revaldinho/cpc_ram_expansion/cpc_ram_expansion/src/old_source/README

This directory contains archived old source code for the original v1.00 board and a modified (cut and rewired) version of that board used to trial the overdrive code.

** NOT TO BE USED WITH THE V1.10 CPLD BOARD **
