revaldinho/cpc_ram_expansion/cpc_eightrom/releases/v1.01/cpc_eightrom_placement.png

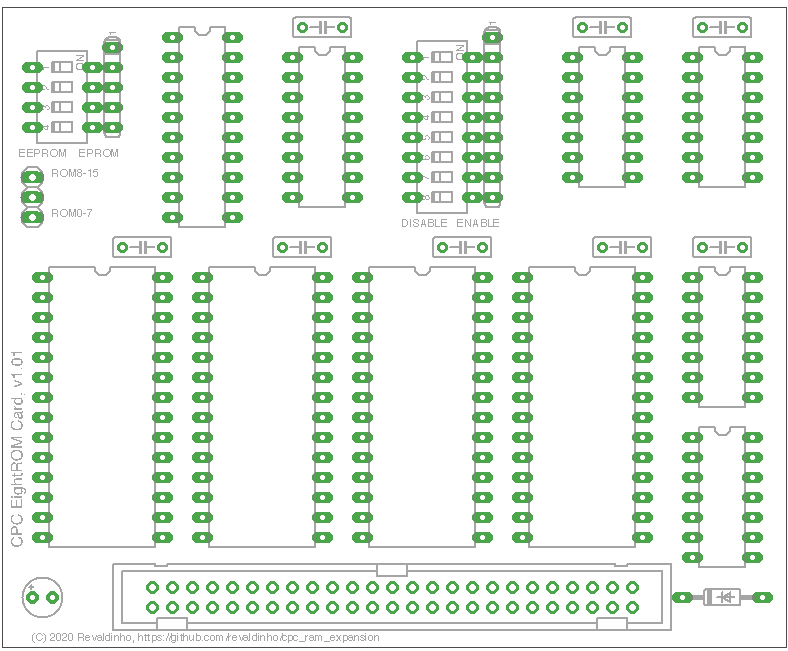
cpc_eightrom/releases/v1.01/cpc_eightrom_placement.png
