revaldinho/cpc_ram_expansion/cpc_eightrom/releases/v1.01/cpc_eightrom_placement_annotated.jpg

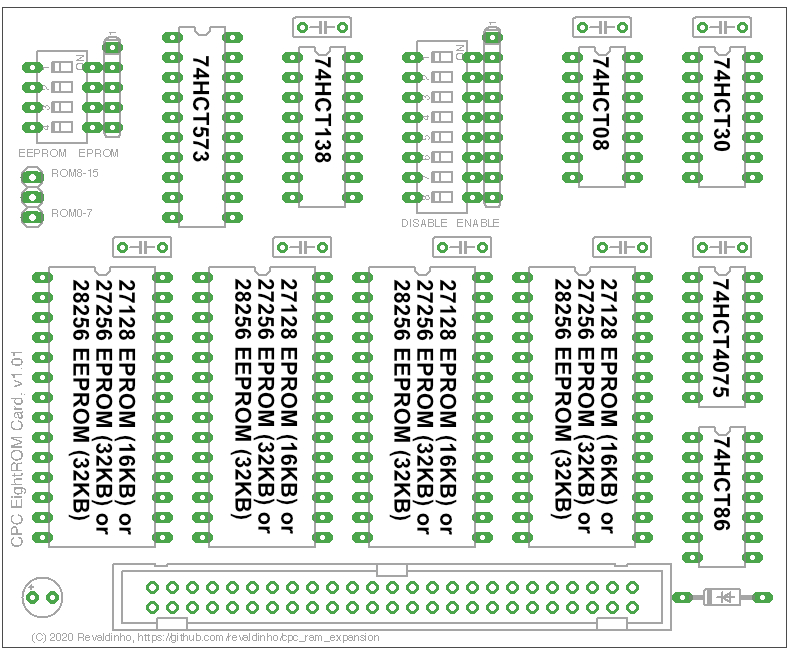
cpc_eightrom/releases/v1.01/cpc_eightrom_placement_annotated.jpg
