revaldinho/cpc_ram_expansion/cpc_ram_expansion1mb/releases/rc-3-canberra/cpc_ram1m_74series/cpc_ram1m_74_v1.00_bot.png

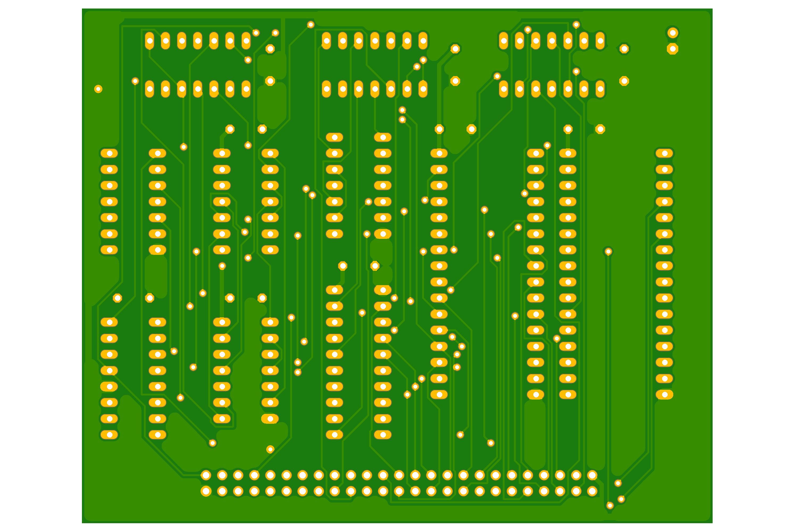
cpc_ram_expansion1mb/releases/rc-3-canberra/cpc_ram1m_74series/cpc_ram1m_74_v1.00_bot.png
