revaldinho/cpc_ram_expansion/cpc_ram_expansion1mb/releases/rc-3-canberra/cpc_ram1m_plcc84/cpc_ram1mb_plcc84_top.png

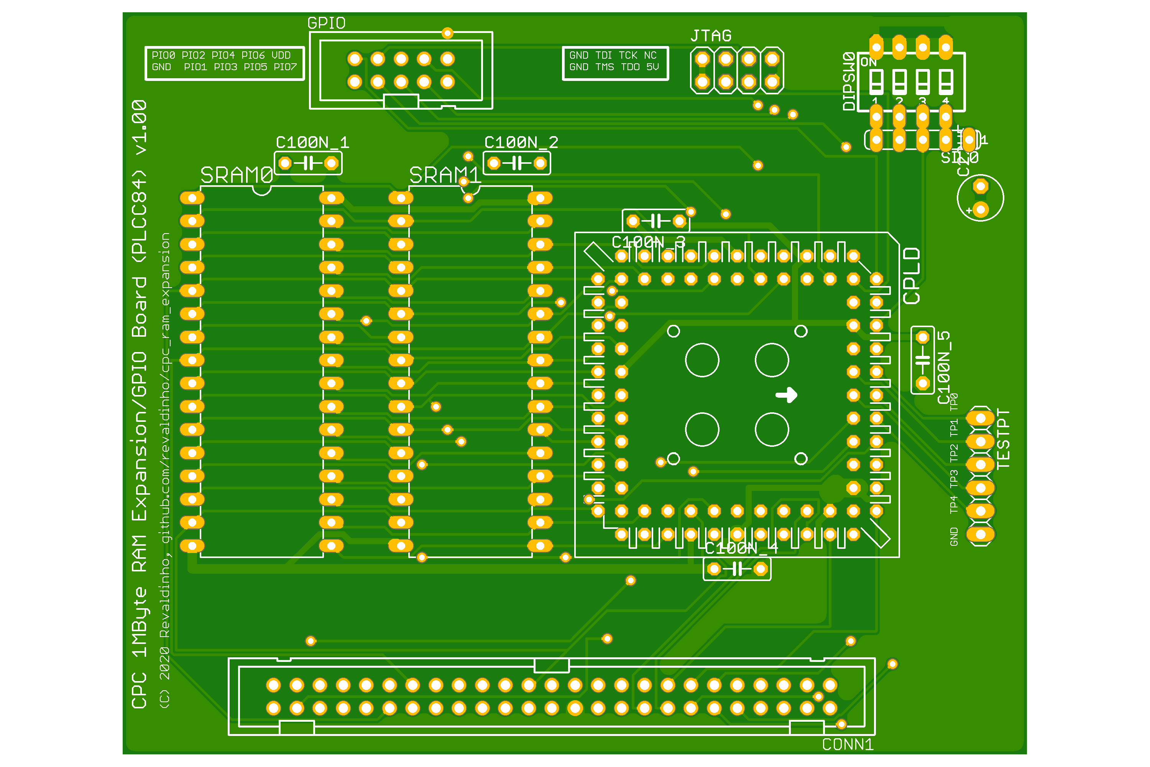
cpc_ram_expansion1mb/releases/rc-3-canberra/cpc_ram1m_plcc84/cpc_ram1mb_plcc84_top.png
