revaldinho/cpc_ram_expansion/img/CPC_1MB_RAM_SN74_photo.jpg

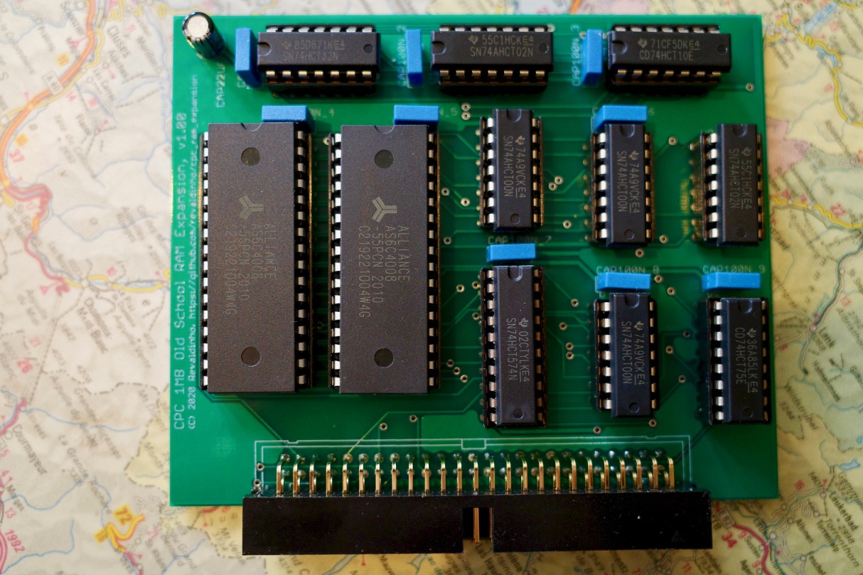
img/CPC_1MB_RAM_SN74_photo.jpg
