revaldinho/cpc_ram_expansion/img/CPC_1MB_RAM_top_v1.00.png

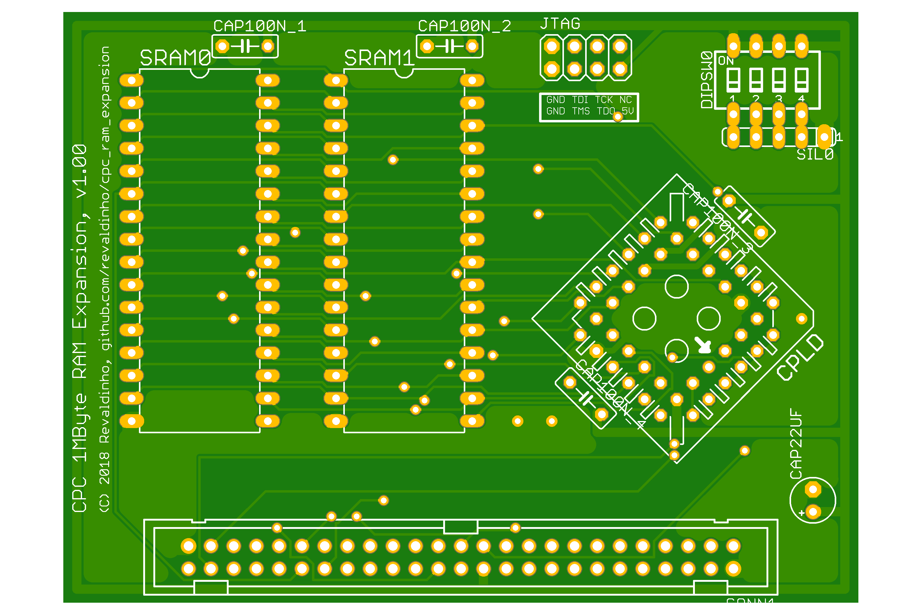
img/CPC_1MB_RAM_top_v1.00.png
