revaldinho/cpc_ram_expansion/img/CPC_512K_RAM_bot_v1.00.png

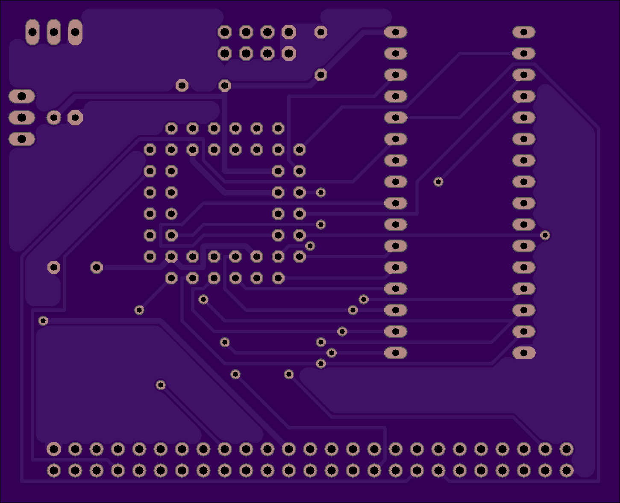
img/CPC_512K_RAM_bot_v1.00.png
