revaldinho/cpc_ram_expansion/img/CPC_512K_RAM_Eagle_top_v1.00.png

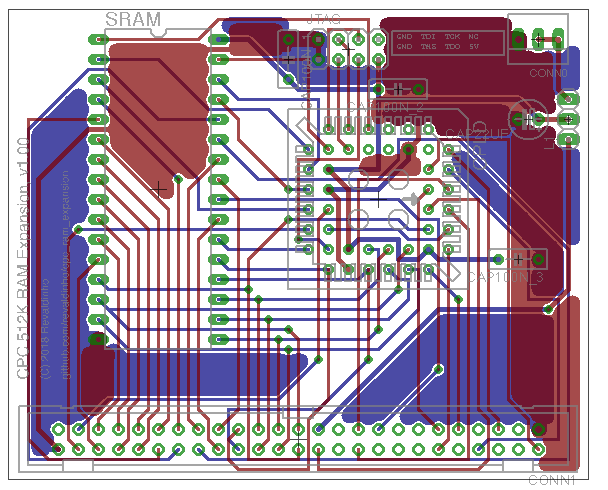
img/CPC_512K_RAM_Eagle_top_v1.00.png
