revaldinho/cpc_ram_expansion/img/CPC_512K_RAM_SN74_bot_v2.01.png

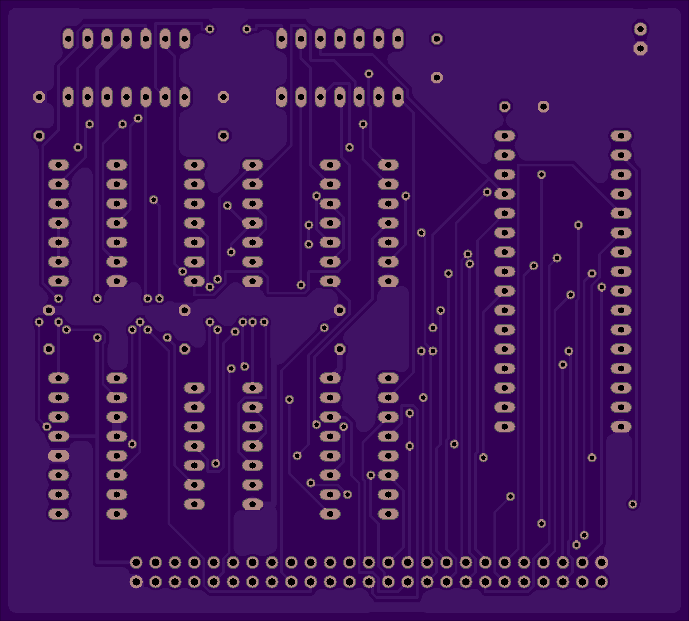
img/CPC_512K_RAM_SN74_bot_v2.01.png
