revaldinho/cpc_ram_expansion/img/CPC_512K_RAM_SN74_photo_v2.01.jpg

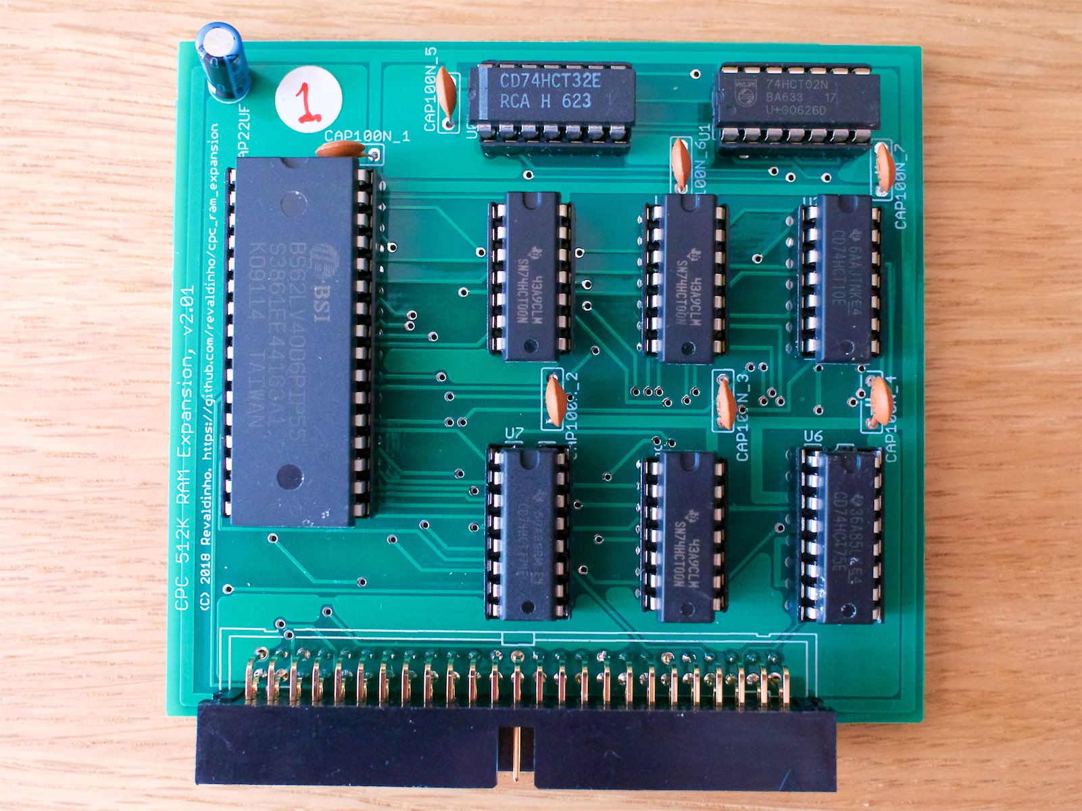
img/CPC_512K_RAM_SN74_photo_v2.01.jpg
