revaldinho/cpc_ram_expansion/img/CPC_512K_RAM_SN74_top_v2.00.png

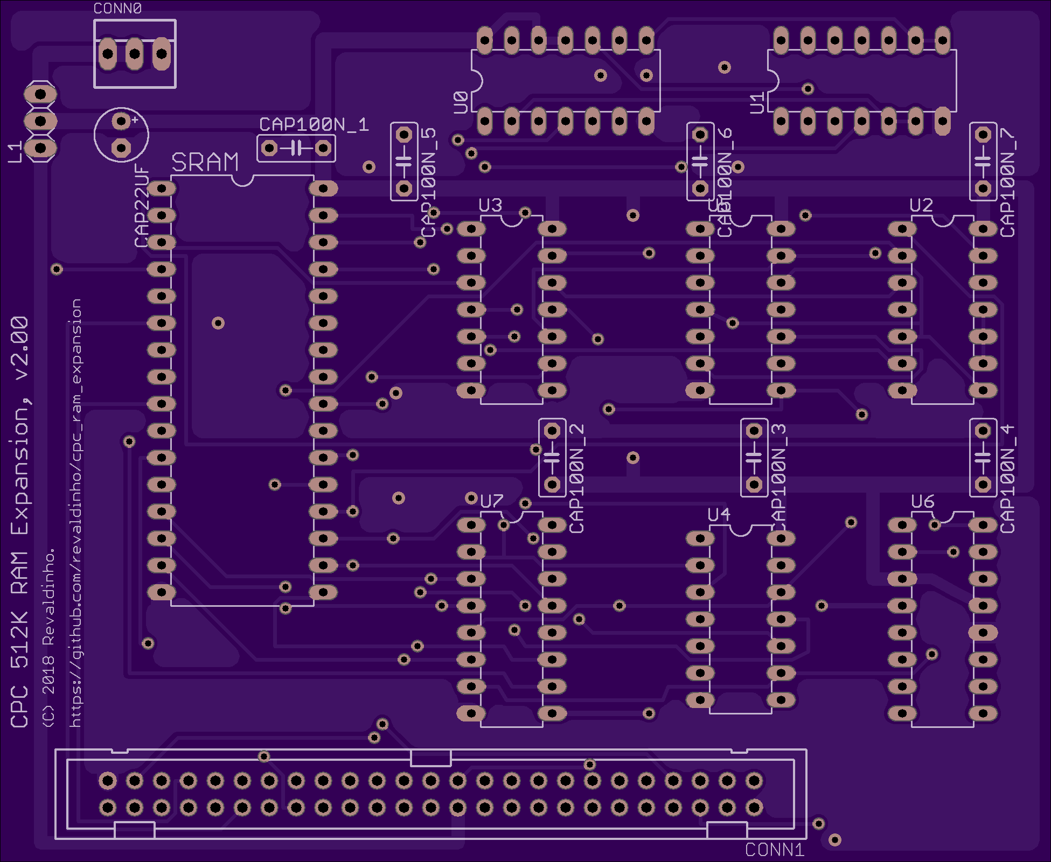
img/CPC_512K_RAM_SN74_top_v2.00.png
