revaldinho/cpc_ram_expansion/img/cpc_backplane_edge.png

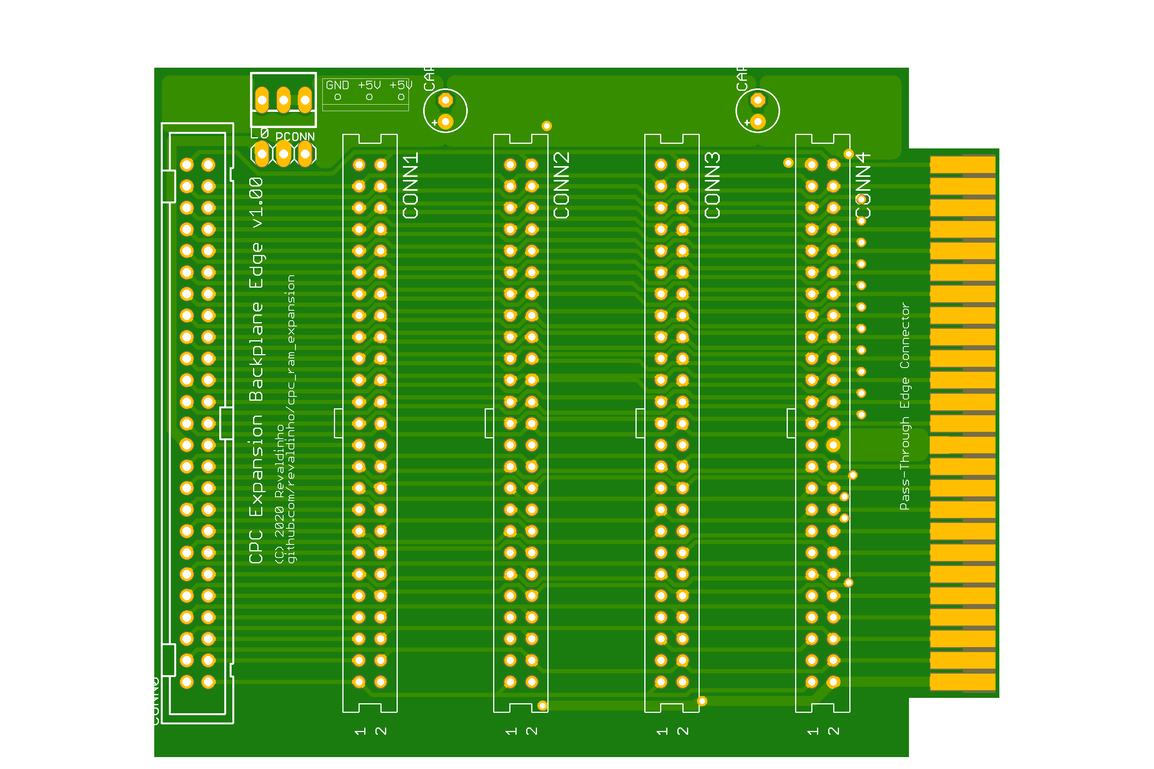
img/cpc_backplane_edge.png
