revaldinho/cpc_ram_expansion/img/cpc_backplane_edge_bot.png

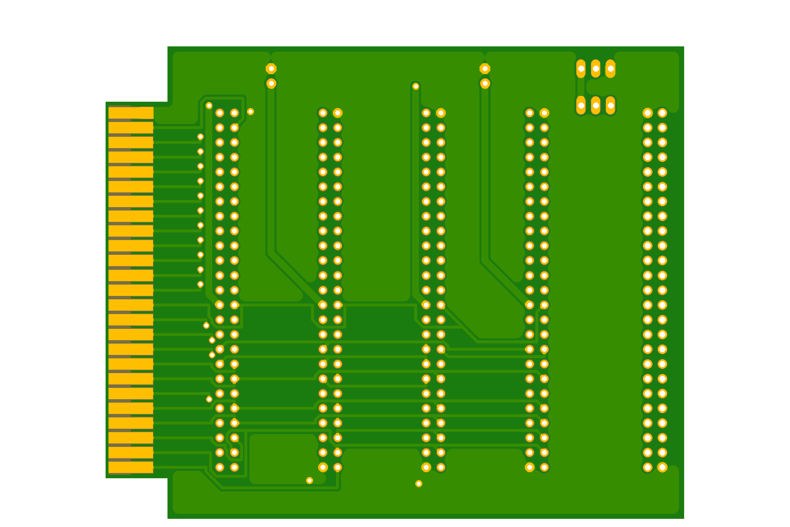
img/cpc_backplane_edge_bot.png
