revaldinho/cpc_ram_expansion/img/CPC_BACKPLANE_placement.png

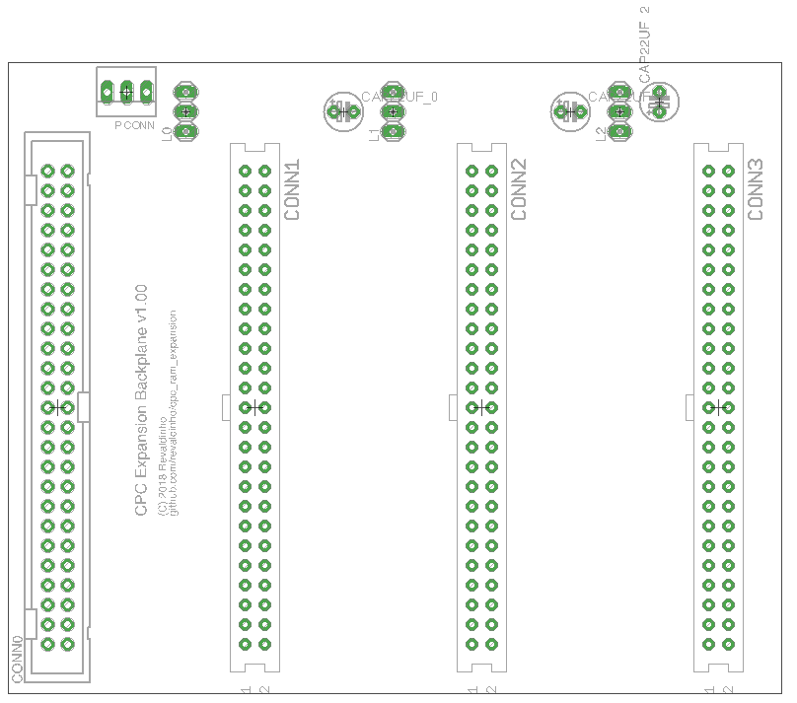
img/CPC_BACKPLANE_placement.png
