revaldinho/cpc_ram_expansion/img/CPC_BACKPLANE_top_v1.00.png

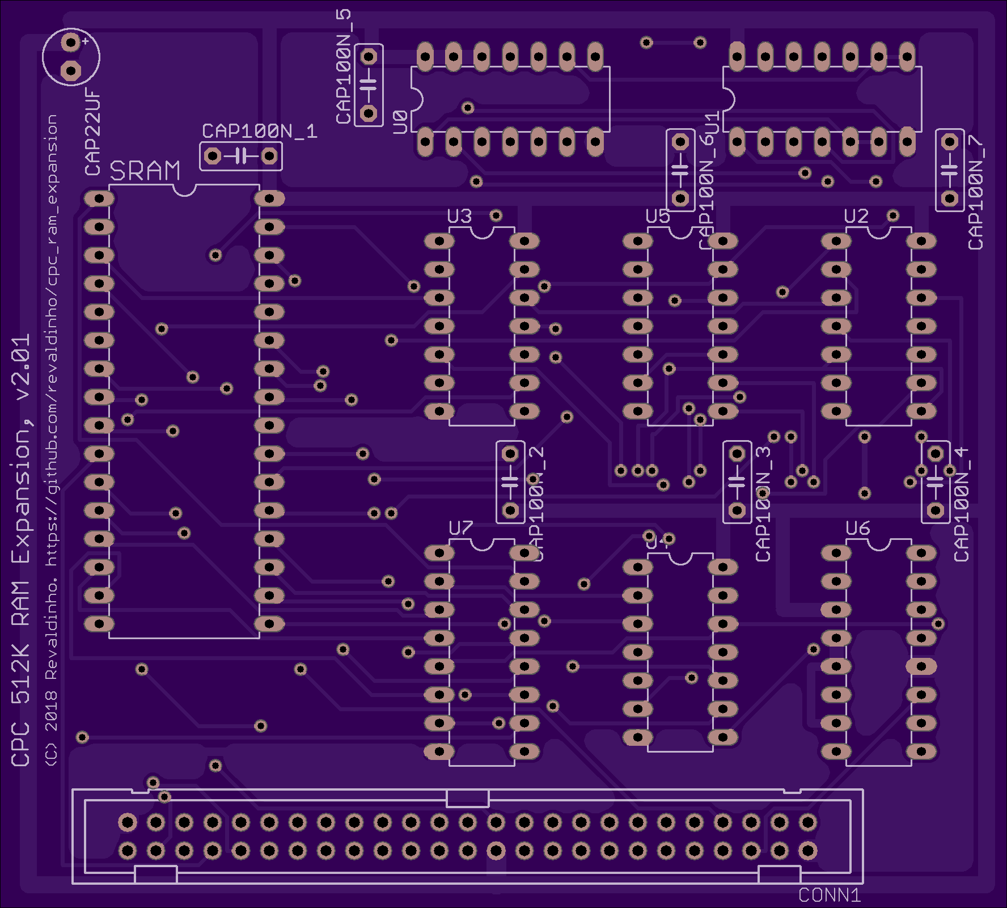
img/CPC_BACKPLANE_top_v1.00.png
