revaldinho/cpc_ram_expansion/img/CPC_BACKPLANE_v1.10_placement.png

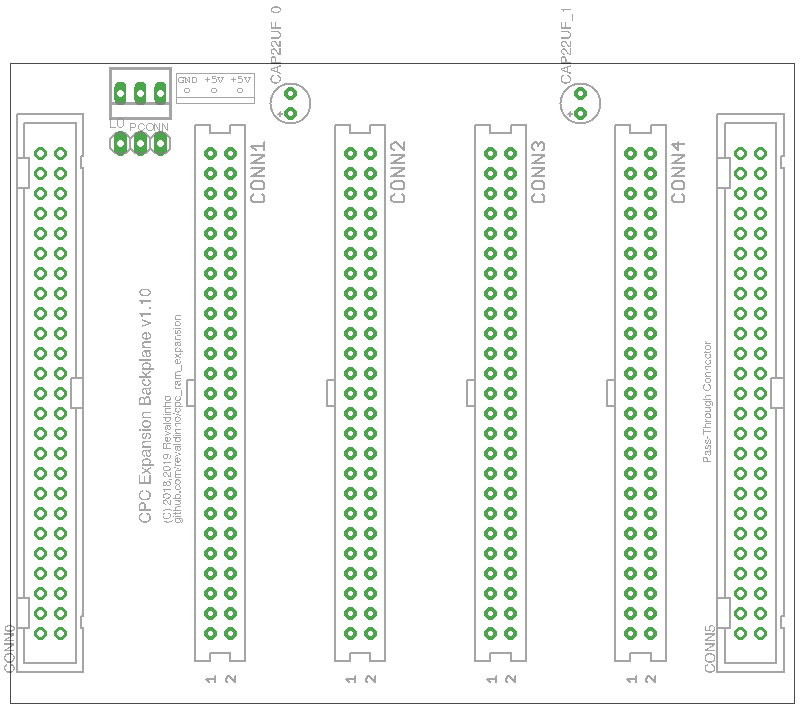
img/CPC_BACKPLANE_v1.10_placement.png
