revaldinho/cpc_ram_expansion/img/CPC_Exp_card_family_photo 1.jpg

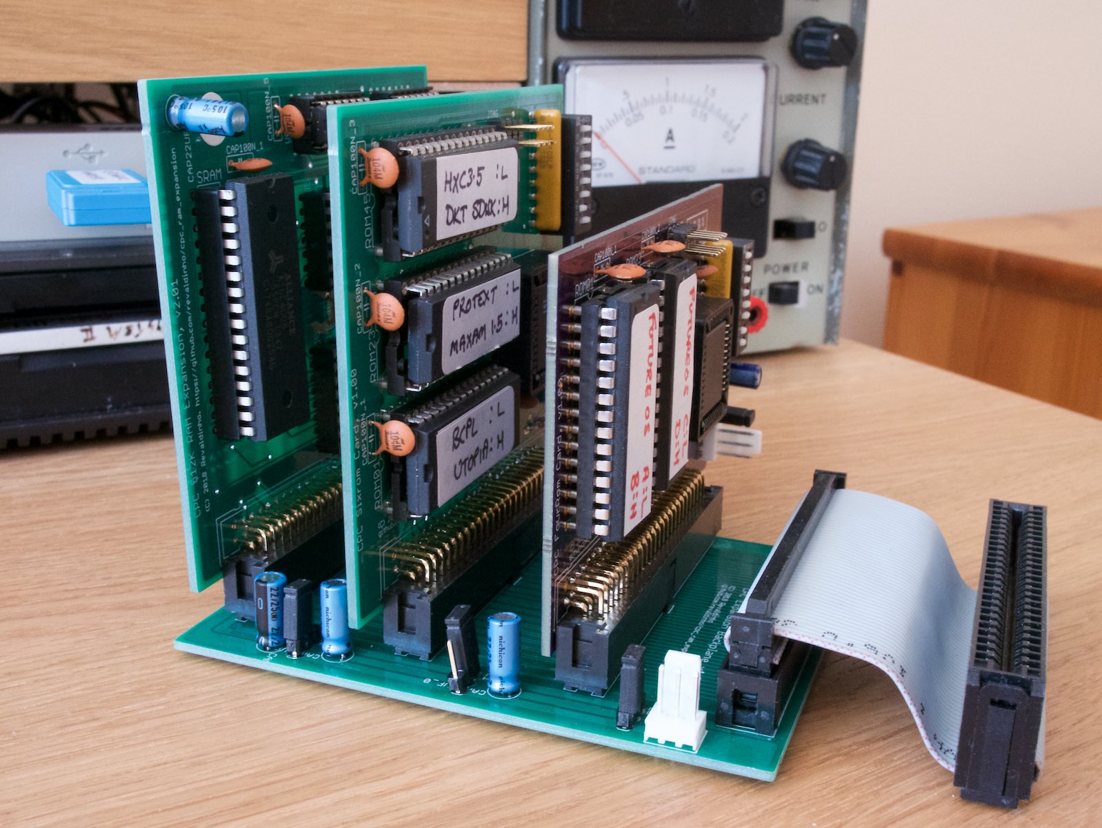
img/CPC_Exp_card_family_photo 1.jpg
