revaldinho/cpc_ram_expansion/img/CPC_Exp_card_family_photo 2.jpg

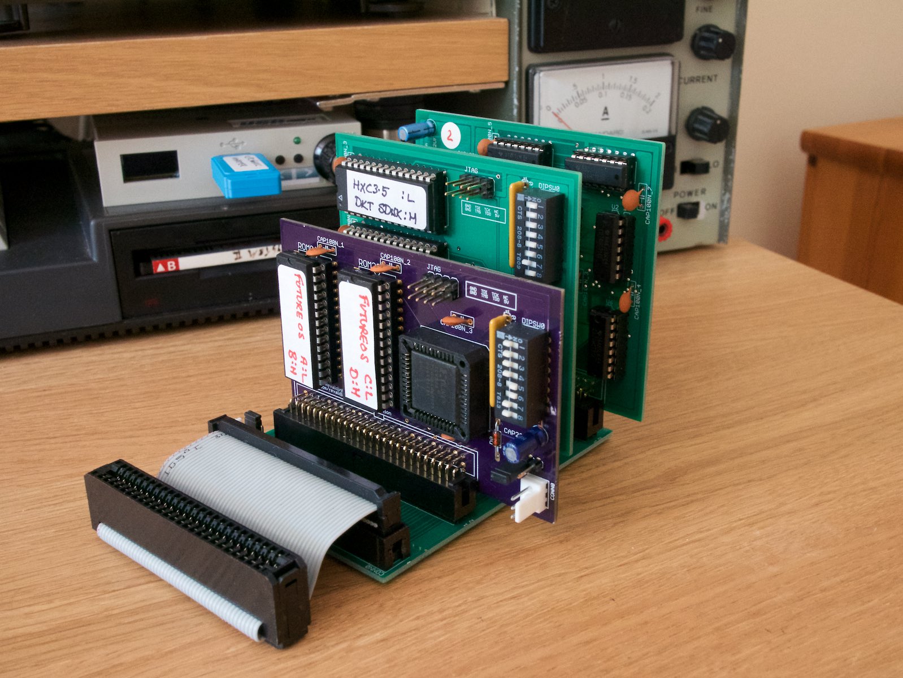
img/CPC_Exp_card_family_photo 2.jpg
