revaldinho/cpc_ram_expansion/img/CPC_FOURROM_bot_V1.00.png

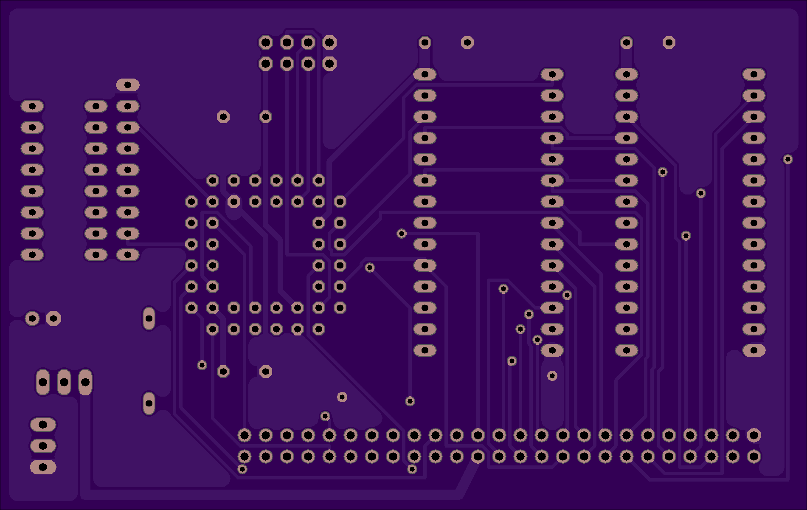
img/CPC_FOURROM_bot_V1.00.png
