revaldinho/cpc_ram_expansion/img/CPC_FOURROM_photo.jpg

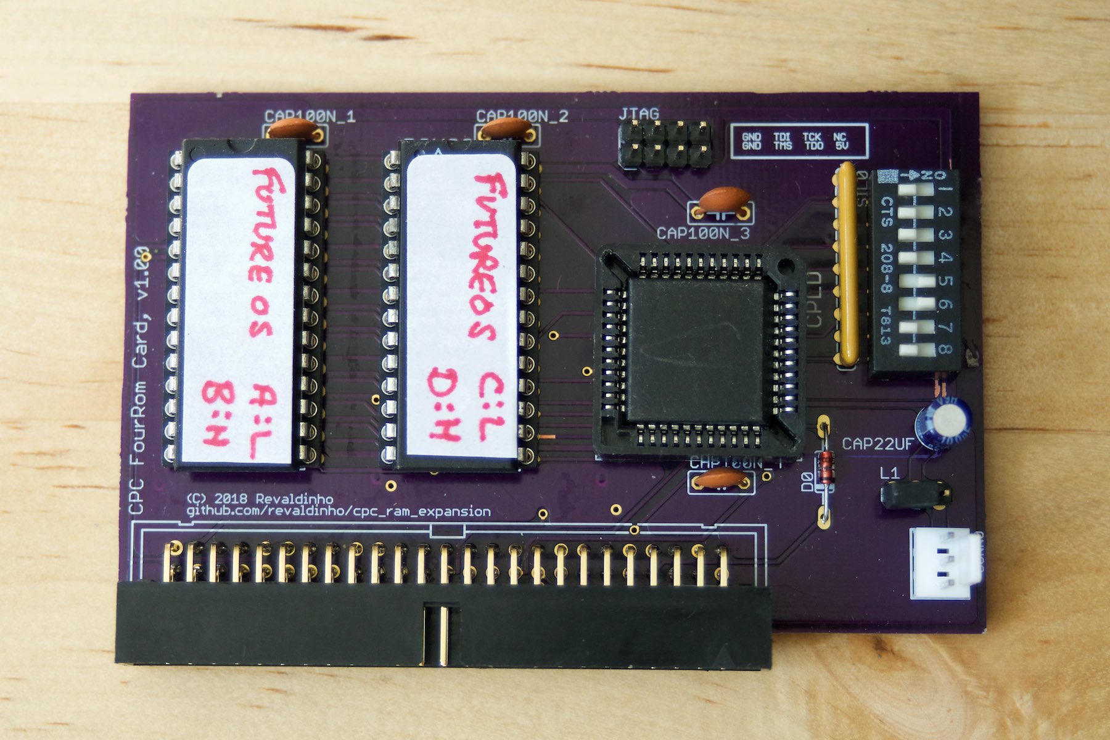
img/CPC_FOURROM_photo.jpg
