revaldinho/cpc_ram_expansion/img/CPC_FOURROM_place.png

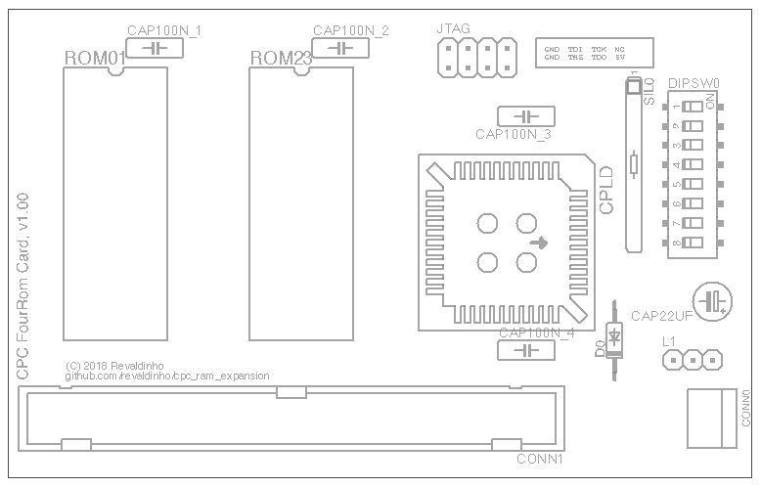
img/CPC_FOURROM_place.png
