revaldinho/cpc_ram_expansion/img/CPC_SIXROM_Eagle_V1.00.png

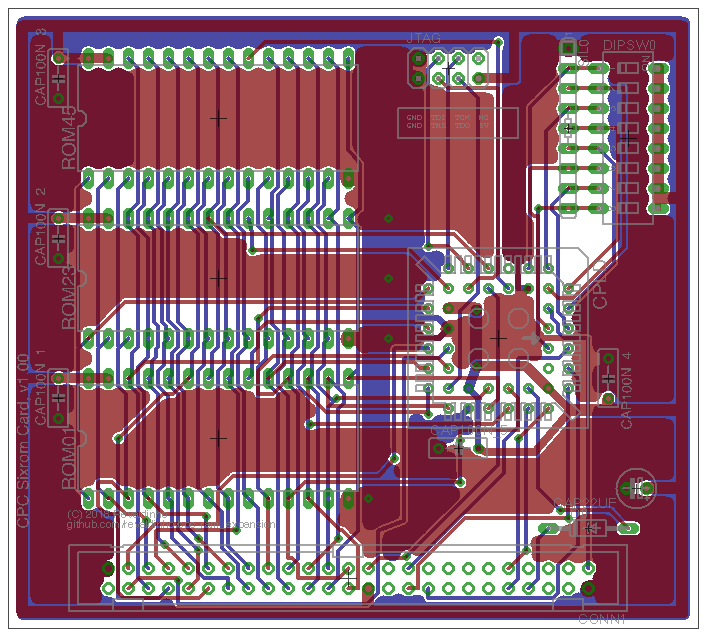
img/CPC_SIXROM_Eagle_V1.00.png
