revaldinho/cpc_ram_expansion/img/CPC_SIXROM_photo1.jpg

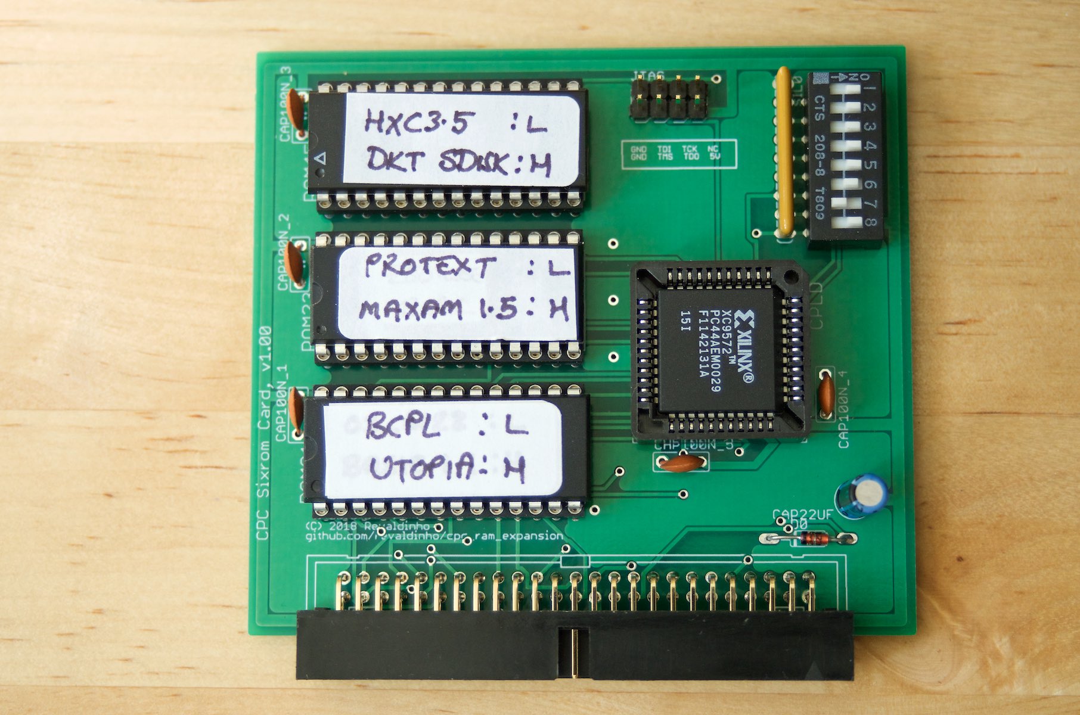
img/CPC_SIXROM_photo1.jpg
