revaldinho/cpc_ram_expansion/img/CPC_SIXROM_V1.00_bot.png

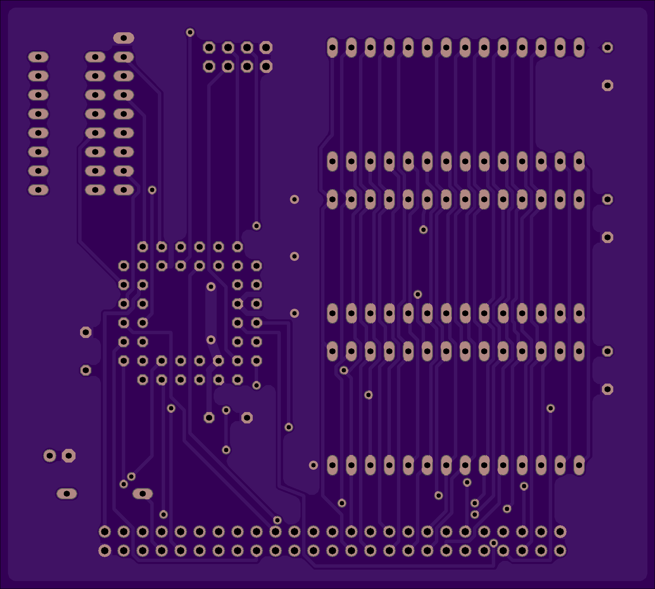
img/CPC_SIXROM_V1.00_bot.png
