revaldinho/cpc_ram_expansion/img/CPC_SIXROM_V1.10_photo.jpg

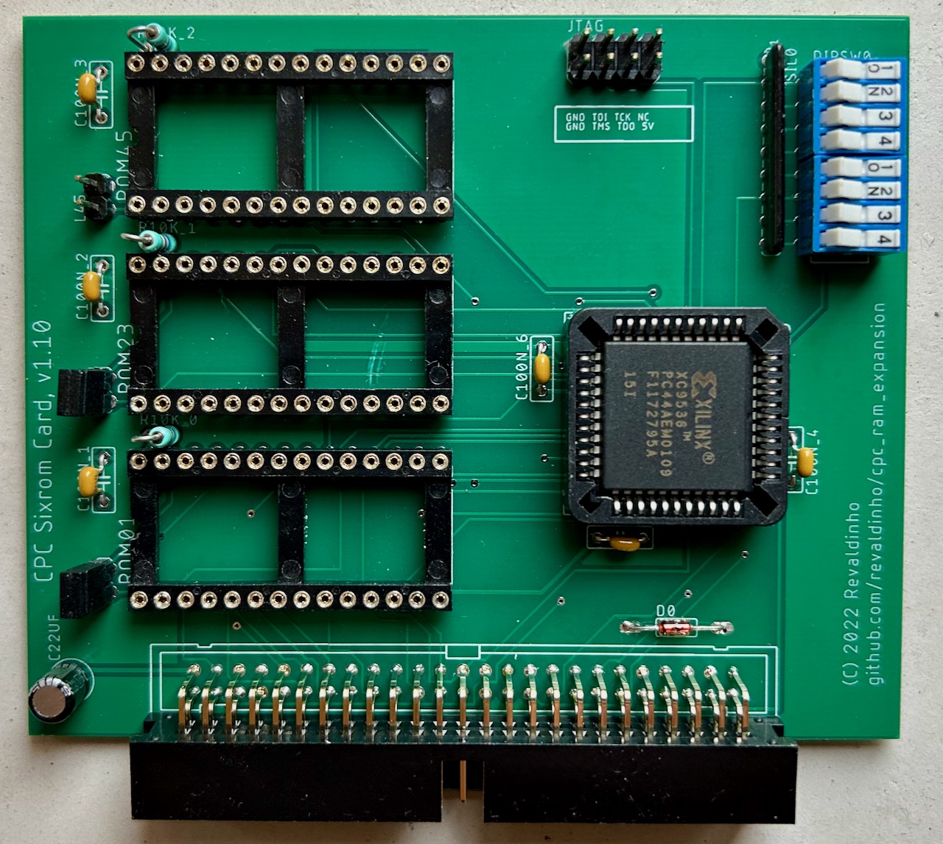
img/CPC_SIXROM_V1.10_photo.jpg
