revaldinho/cpc_ram_expansion/img/CPC_SIXROM_V1.10_place.png

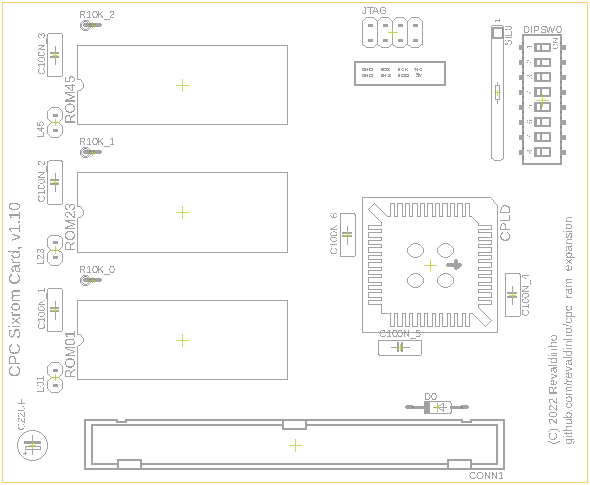
img/CPC_SIXROM_V1.10_place.png
