revaldinho/cpc_ram_expansion/img/CPC_UNIVERSAL_RAM512K.jpg

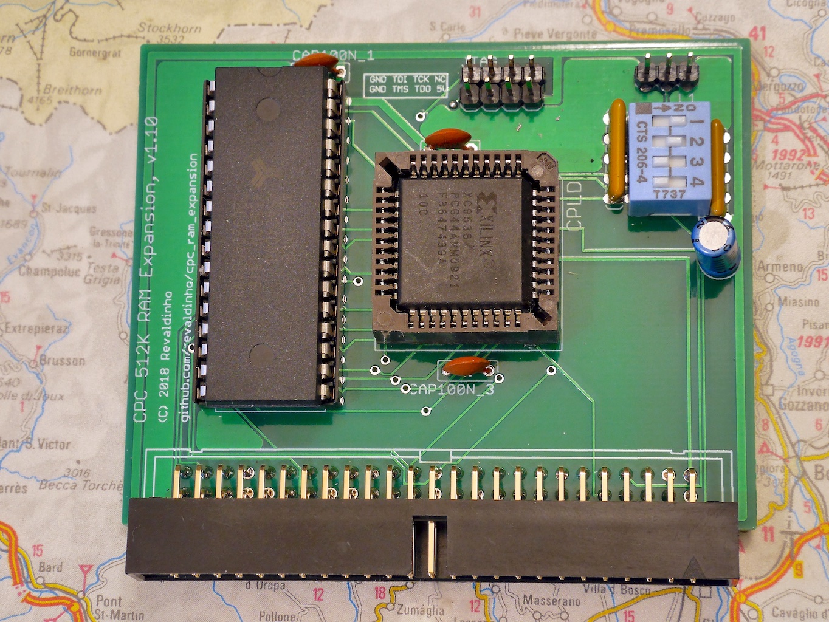
img/CPC_UNIVERSAL_RAM512K.jpg
