revaldinho/cpc_ram_expansion/img/EightROM_board.jpeg

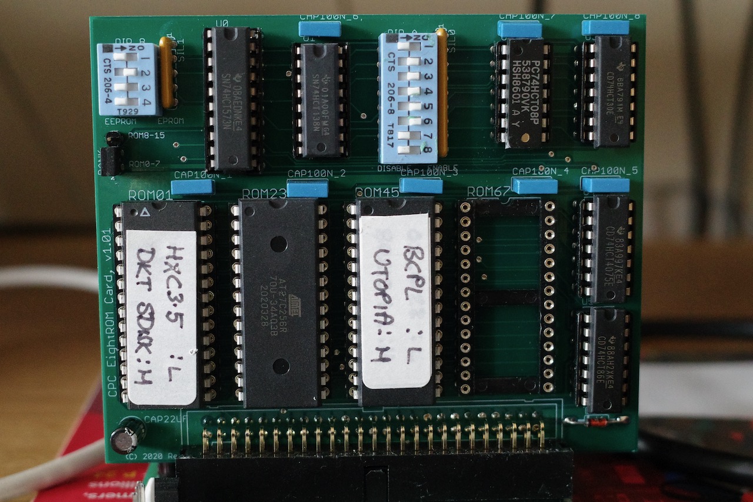
img/EightROM_board.jpeg
