revaldinho/cpc_ram_expansion/img/EightROM_with_display.jpeg

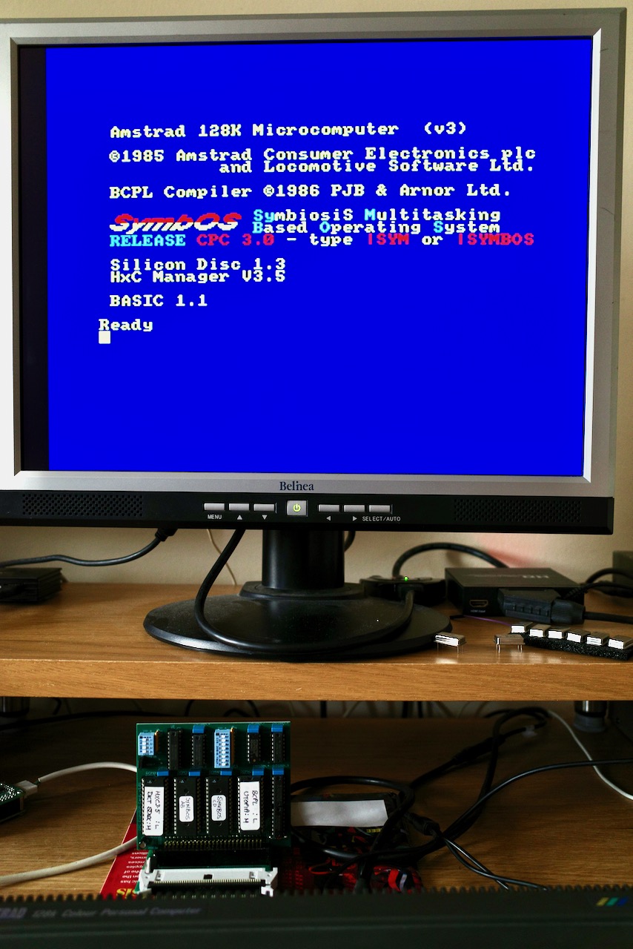
img/EightROM_with_display.jpeg
