revaldinho/cpc_ram_expansion/img/FourSlotEdgeExpansion.jpg

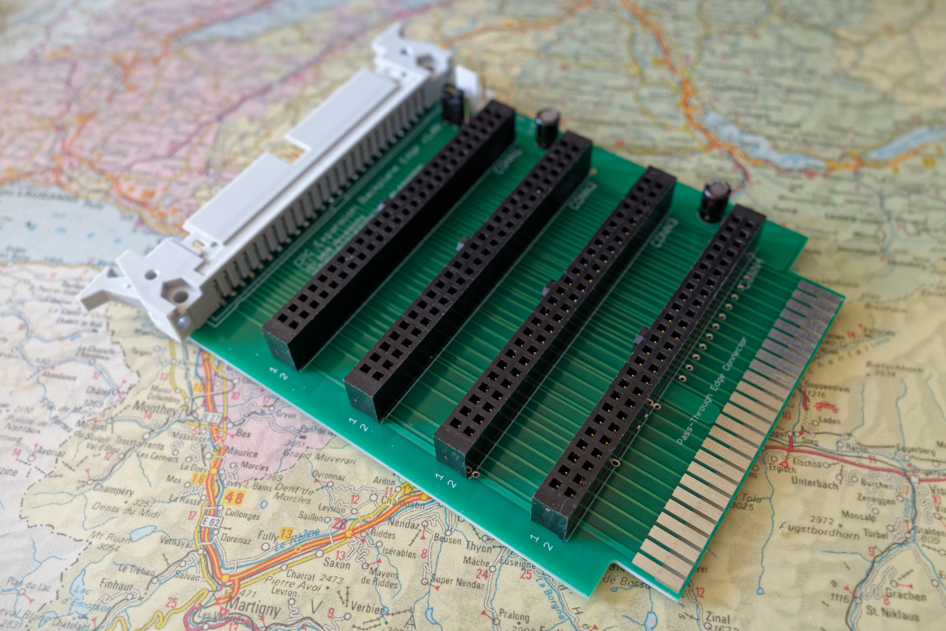
img/FourSlotEdgeExpansion.jpg
