revaldinho/cpc_ram_expansion/img/protoboard.jpg

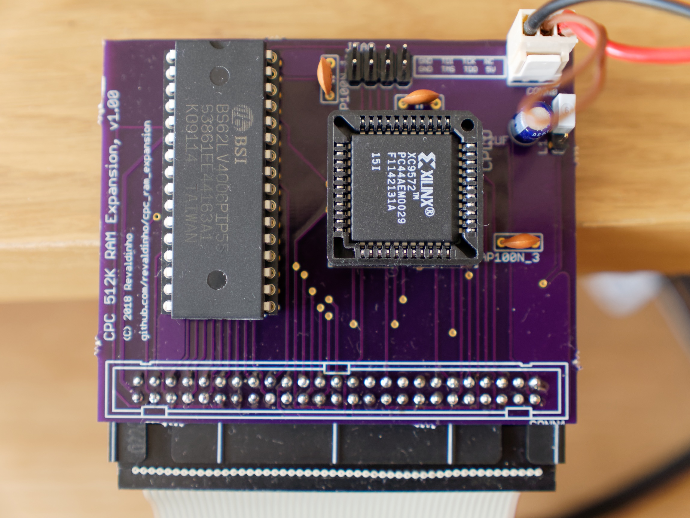
img/protoboard.jpg
