revaldinho/cpc_ram_expansion/img/T35_ROMBOARD_Eagle_V1.00_top.png

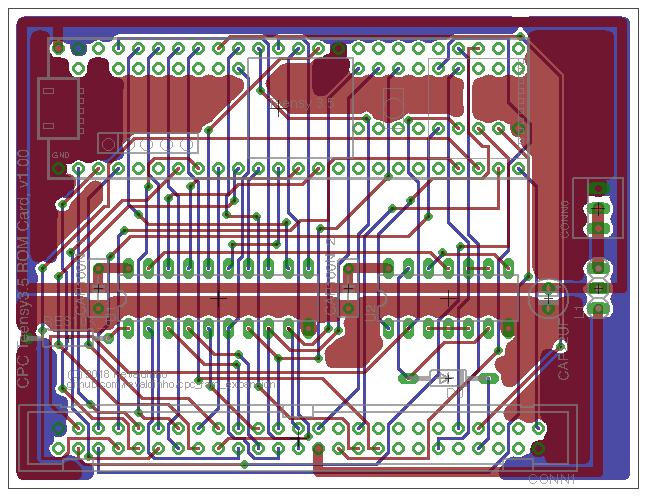
img/T35_ROMBOARD_Eagle_V1.00_top.png
