revaldinho/cpc_ram_expansion/img/T35_ROMBOARD_V1.10_bot.png

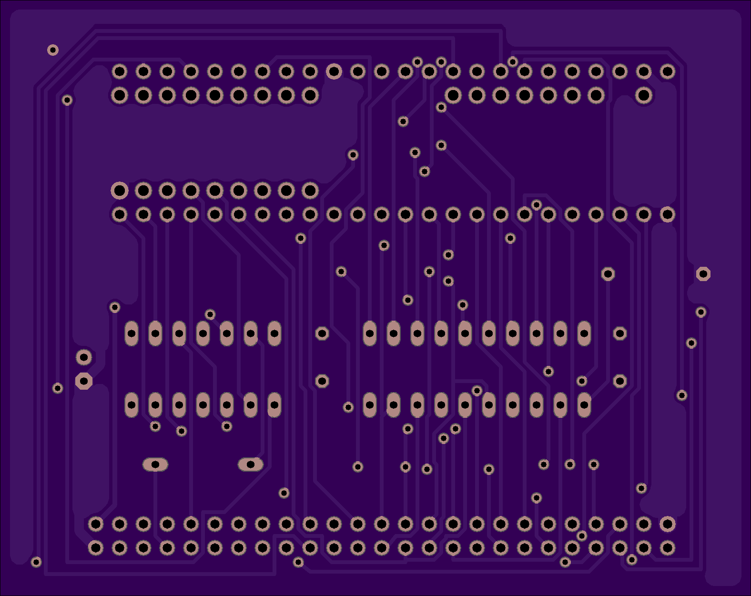
img/T35_ROMBOARD_V1.10_bot.png
