revaldinho/cpc_ram_expansion/cpc_backplane/pcb/cpc_backplane5.v

//
//
// netlister.py format
//
// (c) Revaldinho, 2018
//
//
// Unbuffered board - assume power and signal buffering is done on a dedicated board.
//
// 2018-08-12 Add 4th connector and simplify external power connections

module cpc_backplane5 ();

  // wire declarations
  supply0 VSS;
  supply1 VDD_CPC;
  supply1 VDD_EXT;
  supply1 VDD1;


  special_wire CLK, RESET_B, BUSRESET_B;

  wire Sound;
  wire A15,A14,A13,A12,A11,A10,A9,A8,A7,A6,A5,A4,A3,A2,A1,A0 ;
  wire D7,D6,D5,D4,D3,D2,D1,D0 ;
  wire MREQ_B;
  wire M1_B;
  wire RFSH_B;
  wire IOREQ_B;
  wire RD_B;
  wire WR_B;
  wire HALT_B;
  wire INT_B ;
  wire NMI_B ;
  wire BUSRQ_B;
  wire BUSACK_B;
  wire READY;
  wire ROMEN_B;
  wire ROMDIS ;
  wire RAMRD_B;
  wire RAMDIS;
  wire CURSOR;
  wire LPEN;
  wire EXP_B;





  // 3 pin header with link to use either CPC or external 5V power for the board
  hdr1x03      L0 (
                   .p1(VDD_CPC),
                   .p2(VDD1),
                   .p3(VDD_EXT)
                   );

  PJ057A  PCONN (
                 .centre(VDD_EXT),
                 .barrel1(VSS),
                 .barrel2(VSS)
                 );

//  // Radial electolytics
//  cap22uf         C0(.minus(VSS),.plus(VDD1));
//  cap22uf         C1(.minus(VSS),.plus(VDD1));

  // Amstrad CPC Edge Connector
  //
  // V1.01 Corrected upper and lower rows for male header.

  idc_hdr_50w  CONN0 (
                      .p50(Sound),   .p49(VSS),
                      .p48(A15),     .p47(A14),
                      .p46(A13),     .p45(A12),
                      .p44(A11),     .p43(A10),
                      .p42(A9),      .p41(A8)
                      .p40(A7),      .p39(A6),
                      .p38(A5),      .p37(A4),
                      .p36(A3),      .p35(A2),
                      .p34(A1),      .p33(A0),
                      .p32(D7),      .p31(D6)
                      .p30(D5),      .p29(D4),
                      .p28(D3),      .p27(D2),
                      .p26(D1),      .p25(D0),
                      .p24(VDD_CPC), .p23(MREQ_B),
                      .p22(M1_B),    .p21(RFSH_B),
                      .p20(IOREQ_B), .p19(RD_B),
                      .p18(WR_B),    .p17(HALT_B),
                      .p16(INT_B),   .p15(NMI_B),
                      .p14(BUSRQ_B), .p13(BUSACK_B),
                      .p12(READY),   .p11(BUSRESET_B),
                      .p10(RESET_B), .p9 (ROMEN_B),
                      .p8 (ROMDIS),  .p7 (RAMRD_B),
                      .p6 (RAMDIS),  .p5 (CURSOR),
                      .p4 (LPEN),    .p3 (EXP_B),
                      .p2 (VSS),     .p1 (CLK)
                      ) ;

  // Female sockets have pins reversed by orientation on the board so keep the same
  // logical connections and the male header above.
  idc_skt_50w  CONN1 (
                      .p50(Sound),   .p49(VSS),
                      .p48(A15),     .p47(A14),
                      .p46(A13),     .p45(A12),
                      .p44(A11),     .p43(A10),
                      .p42(A9),      .p41(A8)
                      .p40(A7),      .p39(A6),
                      .p38(A5),      .p37(A4),
                      .p36(A3),      .p35(A2),
                      .p34(A1),      .p33(A0),
                      .p32(D7),      .p31(D6)
                      .p30(D5),      .p29(D4),
                      .p28(D3),      .p27(D2),
                      .p26(D1),      .p25(D0),
                      .p24(VDD1),    .p23(MREQ_B),
                      .p22(M1_B),    .p21(RFSH_B),
                      .p20(IOREQ_B), .p19(RD_B),
                      .p18(WR_B),    .p17(HALT_B),
                      .p16(INT_B),   .p15(NMI_B),
                      .p14(BUSRQ_B), .p13(BUSACK_B),
                      .p12(READY),   .p11(BUSRESET_B),
                      .p10(RESET_B), .p9 (ROMEN_B),
                      .p8 (ROMDIS),  .p7 (RAMRD_B),
                      .p6 (RAMDIS),  .p5 (CURSOR),
                      .p4 (LPEN),    .p3 (EXP_B),
                      .p2 (VSS),     .p1 (CLK)
                      ) ;
  idc_skt_50w  CONN2 (
                      .p50(Sound),   .p49(VSS),
                      .p48(A15),     .p47(A14),
                      .p46(A13),     .p45(A12),
                      .p44(A11),     .p43(A10),
                      .p42(A9),      .p41(A8)
                      .p40(A7),      .p39(A6),
                      .p38(A5),      .p37(A4),
                      .p36(A3),      .p35(A2),
                      .p34(A1),      .p33(A0),
                      .p32(D7),      .p31(D6)
                      .p30(D5),      .p29(D4),
                      .p28(D3),      .p27(D2),
                      .p26(D1),      .p25(D0),
                      .p24(VDD1),    .p23(MREQ_B),
                      .p22(M1_B),    .p21(RFSH_B),
                      .p20(IOREQ_B), .p19(RD_B),
                      .p18(WR_B),    .p17(HALT_B),
                      .p16(INT_B),   .p15(NMI_B),
                      .p14(BUSRQ_B), .p13(BUSACK_B),
                      .p12(READY),   .p11(BUSRESET_B),
                      .p10(RESET_B), .p9 (ROMEN_B),
                      .p8 (ROMDIS),  .p7 (RAMRD_B),
                      .p6 (RAMDIS),  .p5 (CURSOR),
                      .p4 (LPEN),    .p3 (EXP_B),
                      .p2 (VSS),     .p1 (CLK)
                      ) ;
  idc_skt_50w  CONN3 (
                      .p50(Sound),   .p49(VSS),
                      .p48(A15),     .p47(A14),
                      .p46(A13),     .p45(A12),
                      .p44(A11),     .p43(A10),
                      .p42(A9),      .p41(A8)
                      .p40(A7),      .p39(A6),
                      .p38(A5),      .p37(A4),
                      .p36(A3),      .p35(A2),
                      .p34(A1),      .p33(A0),
                      .p32(D7),      .p31(D6)
                      .p30(D5),      .p29(D4),
                      .p28(D3),      .p27(D2),
                      .p26(D1),      .p25(D0),
                      .p24(VDD1),    .p23(MREQ_B),
                      .p22(M1_B),    .p21(RFSH_B),
                      .p20(IOREQ_B), .p19(RD_B),
                      .p18(WR_B),    .p17(HALT_B),
                      .p16(INT_B),   .p15(NMI_B),
                      .p14(BUSRQ_B), .p13(BUSACK_B),
                      .p12(READY),   .p11(BUSRESET_B),
                      .p10(RESET_B), .p9 (ROMEN_B),
                      .p8 (ROMDIS),  .p7 (RAMRD_B),
                      .p6 (RAMDIS),  .p5 (CURSOR),
                      .p4 (LPEN),    .p3 (EXP_B),
                      .p2 (VSS),     .p1 (CLK)
                      ) ;

  idc_skt_50w  CONN4 (
                      .p50(Sound),   .p49(VSS),
                      .p48(A15),     .p47(A14),
                      .p46(A13),     .p45(A12),
                      .p44(A11),     .p43(A10),
                      .p42(A9),      .p41(A8)
                      .p40(A7),      .p39(A6),
                      .p38(A5),      .p37(A4),
                      .p36(A3),      .p35(A2),
                      .p34(A1),      .p33(A0),
                      .p32(D7),      .p31(D6)
                      .p30(D5),      .p29(D4),
                      .p28(D3),      .p27(D2),
                      .p26(D1),      .p25(D0),
                      .p24(VDD1),    .p23(MREQ_B),
                      .p22(M1_B),    .p21(RFSH_B),
                      .p20(IOREQ_B), .p19(RD_B),
                      .p18(WR_B),    .p17(HALT_B),
                      .p16(INT_B),   .p15(NMI_B),
                      .p14(BUSRQ_B), .p13(BUSACK_B),
                      .p12(READY),   .p11(BUSRESET_B),
                      .p10(RESET_B), .p9 (ROMEN_B),
                      .p8 (ROMDIS),  .p7 (RAMRD_B),
                      .p6 (RAMDIS),  .p5 (CURSOR),
                      .p4 (LPEN),    .p3 (EXP_B),
                      .p2 (VSS),     .p1 (CLK)
                      ) ;

  idc_skt_50w  CONN5 (
                      .p50(Sound),   .p49(VSS),
                      .p48(A15),     .p47(A14),
                      .p46(A13),     .p45(A12),
                      .p44(A11),     .p43(A10),
                      .p42(A9),      .p41(A8)
                      .p40(A7),      .p39(A6),
                      .p38(A5),      .p37(A4),
                      .p36(A3),      .p35(A2),
                      .p34(A1),      .p33(A0),
                      .p32(D7),      .p31(D6)
                      .p30(D5),      .p29(D4),
                      .p28(D3),      .p27(D2),
                      .p26(D1),      .p25(D0),
                      .p24(VDD1),    .p23(MREQ_B),
                      .p22(M1_B),    .p21(RFSH_B),
                      .p20(IOREQ_B), .p19(RD_B),
                      .p18(WR_B),    .p17(HALT_B),
                      .p16(INT_B),   .p15(NMI_B),
                      .p14(BUSRQ_B), .p13(BUSACK_B),
                      .p12(READY),   .p11(BUSRESET_B),
                      .p10(RESET_B), .p9 (ROMEN_B),
                      .p8 (ROMDIS),  .p7 (RAMRD_B),
                      .p6 (RAMDIS),  .p5 (CURSOR),
                      .p4 (LPEN),    .p3 (EXP_B),
                      .p2 (VSS),     .p1 (CLK)
                      ) ;


  endmodule
